Red-Singularity/Led_SnowBoards/_Dustin/media/med.jpg

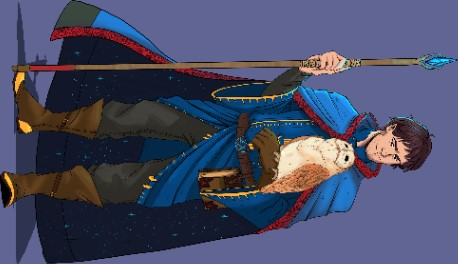
_Dustin/media/med.jpg
