Red-Singularity/Led_SnowBoards/_Dustin/media/mememe.gif

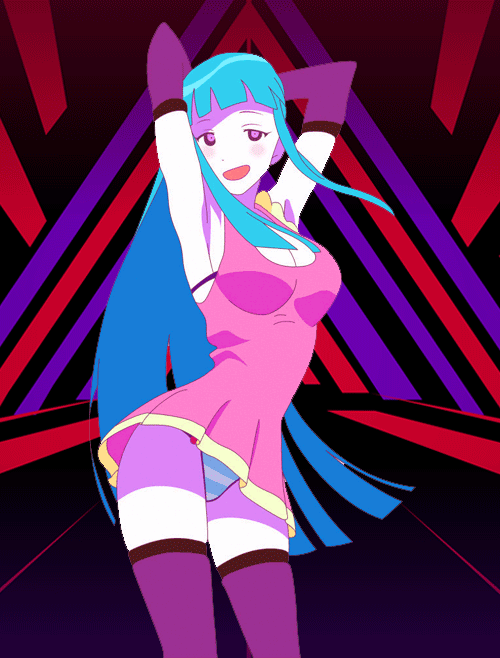
_Dustin/media/mememe.gif
