Red-Singularity/Led_SnowBoards/_Dustin/App Layout V1.png

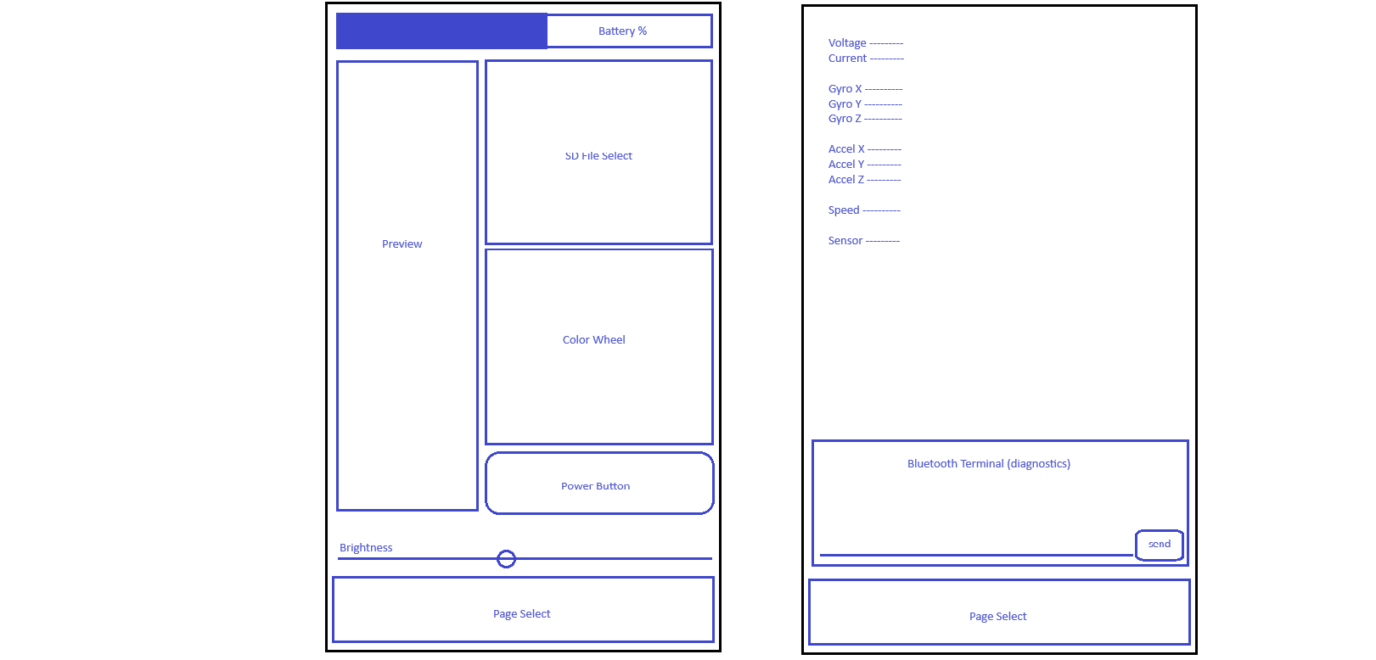
_Dustin/App Layout V1.png
