Red-Singularity/Led_SnowBoards/_Dustin/App Layout V2.jpg

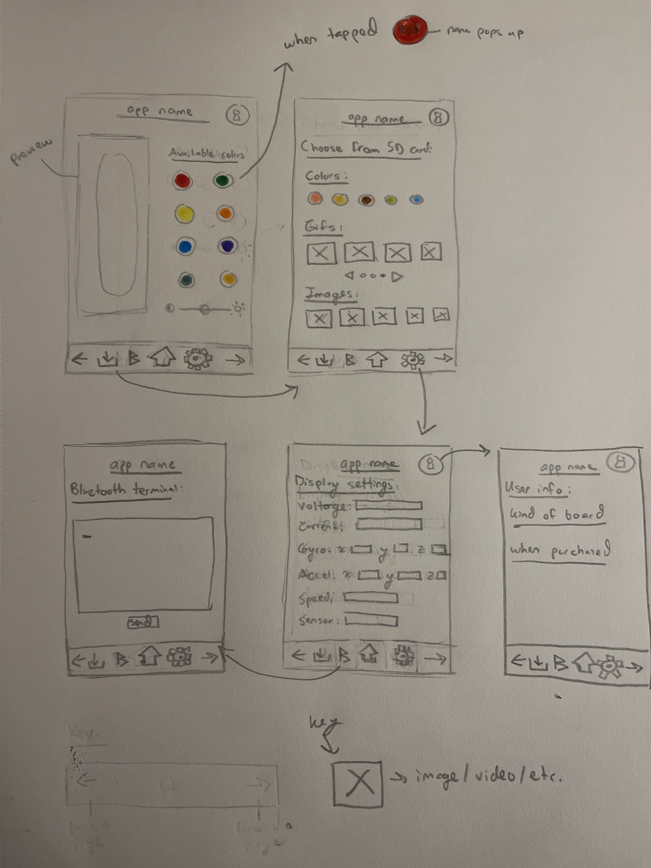
_Dustin/App Layout V2.jpg
