Red-Singularity/Led_SnowBoards/_Dustin/media/amogus.gif

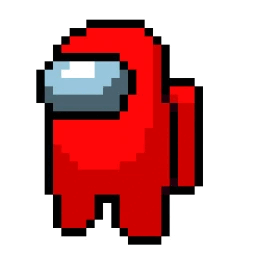
_Dustin/media/amogus.gif
