Red-Singularity/Led_SnowBoards/_Dustin/media/colorwheel.gif

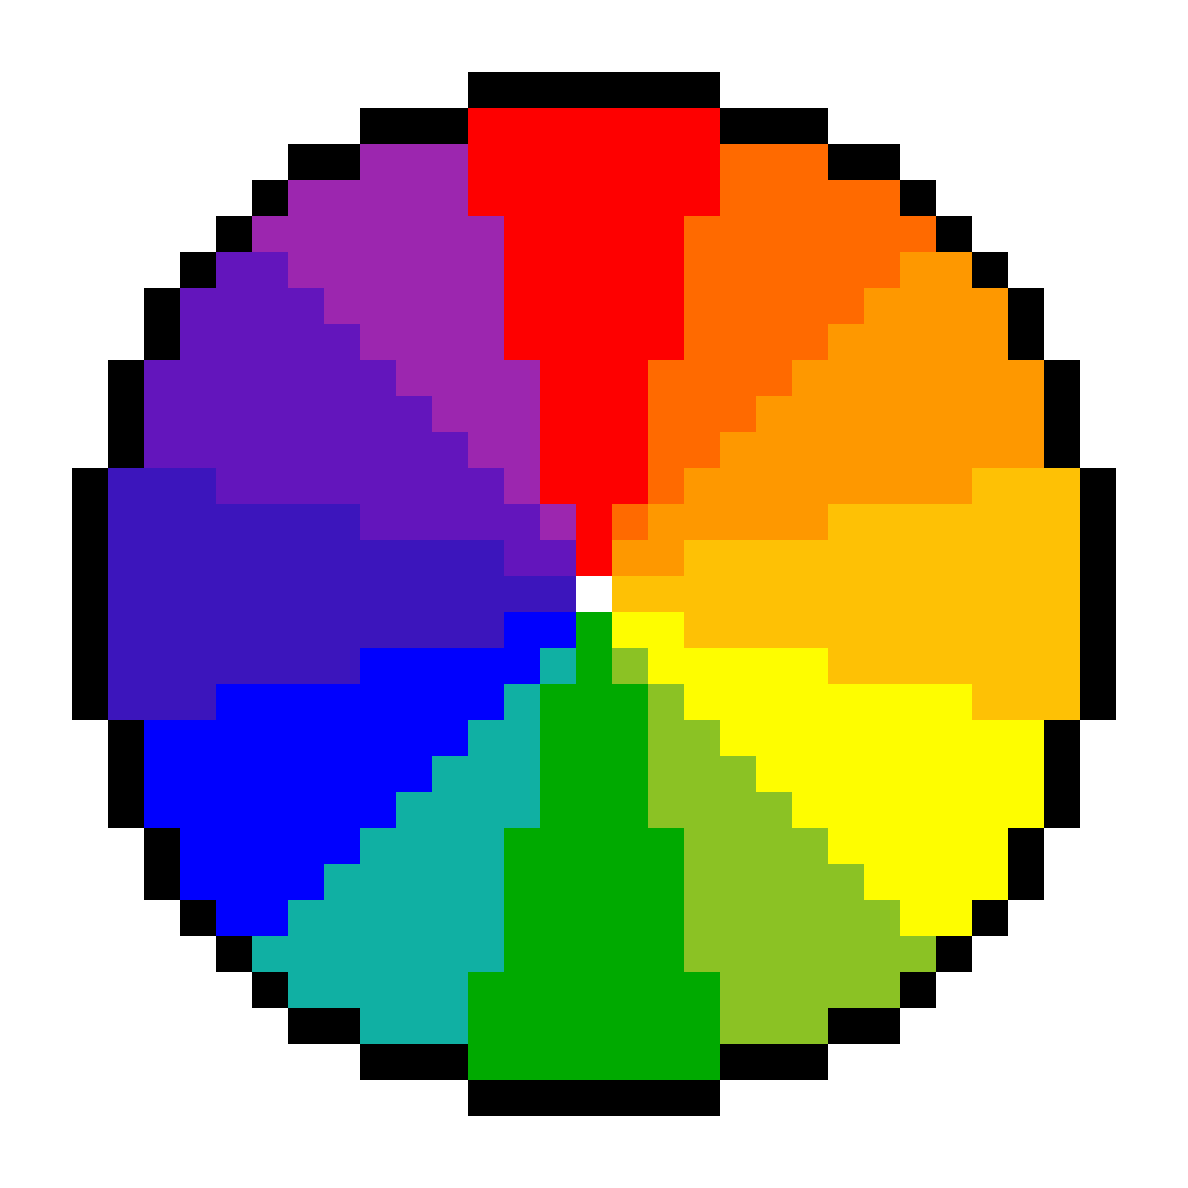
_Dustin/media/colorwheel.gif
