Red-Singularity/Led_SnowBoards/_Dustin/media/link16bit.png

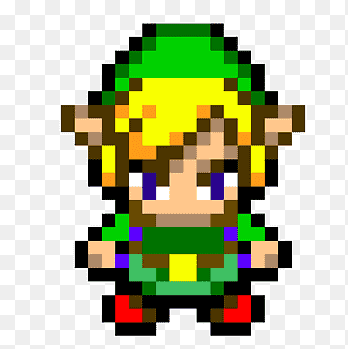
_Dustin/media/link16bit.png
