Red-Singularity/Led_SnowBoards/_Dustin/media/link.png

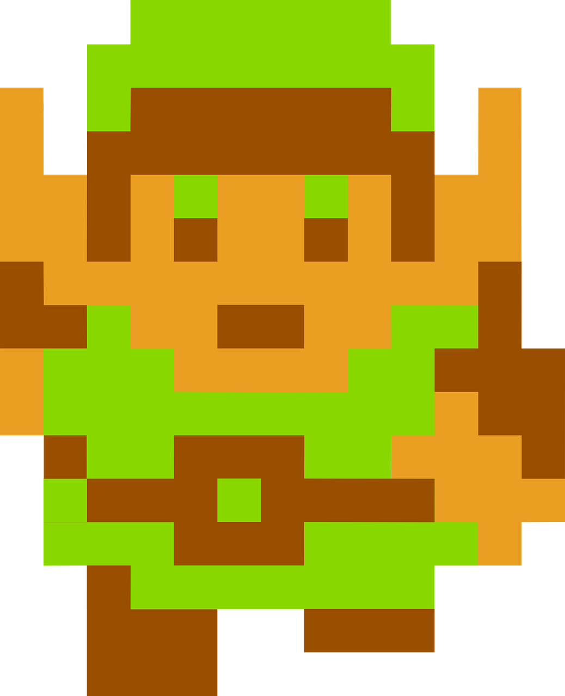
_Dustin/media/link.png
