Red-Singularity/Led_SnowBoards/_Dustin/media/link_s.png

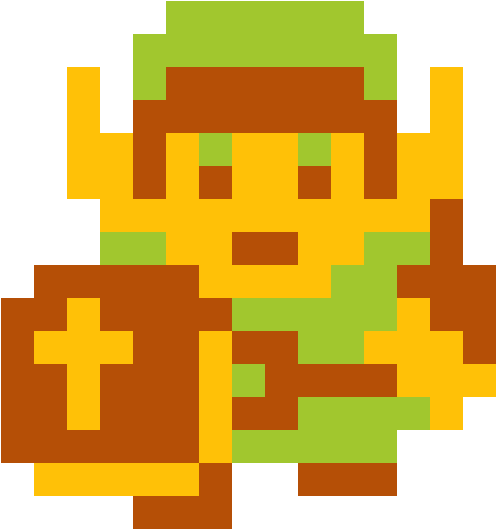
_Dustin/media/link_s.png
