Red-Singularity/Led_SnowBoards/_Dustin/media/mario_characters.gif

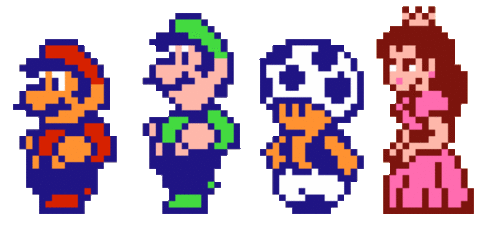
_Dustin/media/mario_characters.gif
