Red-Singularity/Led_SnowBoards/_Dustin/media/rainbow_circle.gif

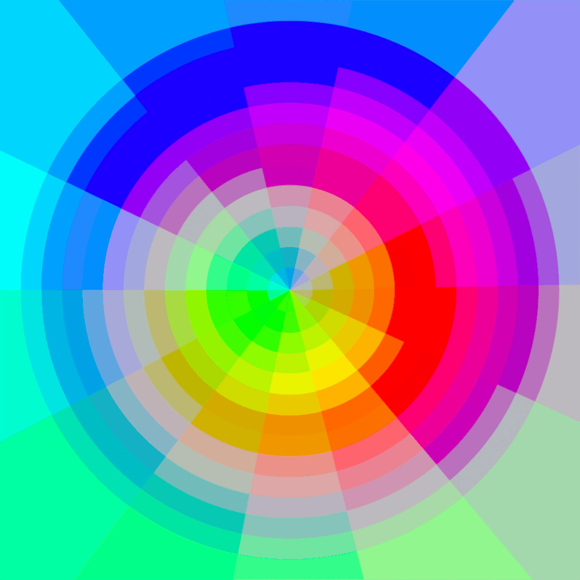
_Dustin/media/rainbow_circle.gif
