Red-Singularity/Led_SnowBoards/_Dustin/media/toothless-dancing.gif

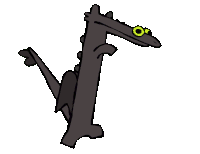
_Dustin/media/toothless-dancing.gif
