Red-Singularity/Led_SnowBoards/_Tim/Snowboard Emulator/processed_Nyan Cat 2.gif

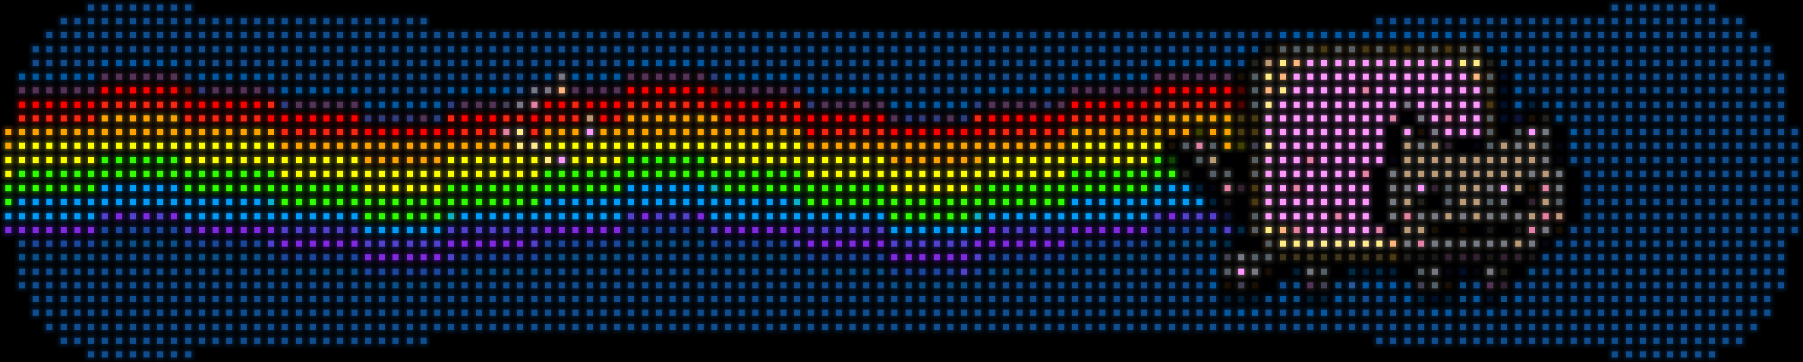
_Tim/Snowboard Emulator/processed_Nyan Cat 2.gif
