Red-Singularity/Led_SnowBoards/_Tim/Snowboard Emulator/Template.png

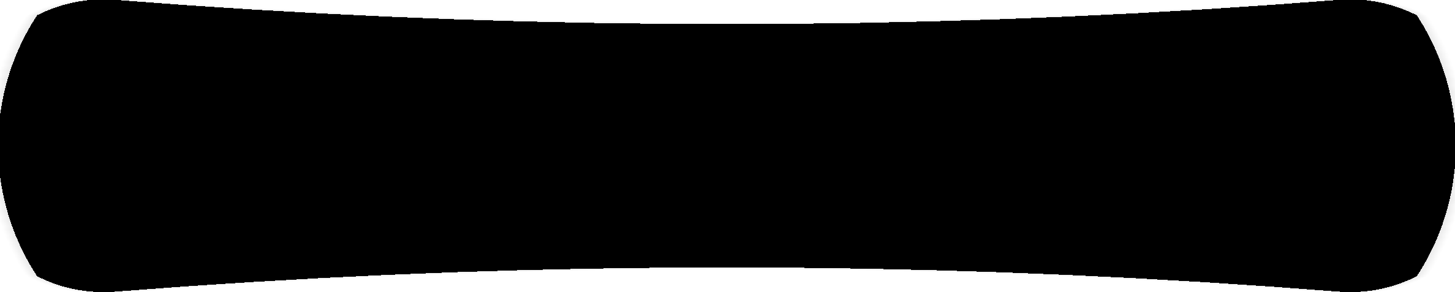
_Tim/Snowboard Emulator/Template.png
