Red-Singularity/Led_SnowBoards/_Dustin/media/test.png

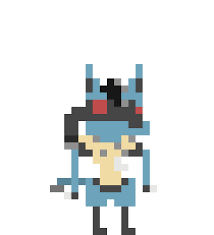
_Dustin/media/test.png
