Red-Singularity/Led_SnowBoards/_Dustin/arduino/sketches/led_snowboard_v2/gif_assignment.ino

void assign_media1(){
  readFrame("media1");
  FastLED.show();
}

void assign_media2(){
  // assign mario from sd card
  readFrame("media2");
  FastLED.show();
}


void assign_media3(){
  // assign pacman from sd card
  readFrame("media3");
  FastLED.show();
}

void assign_media4(){
  // assign neon board from sd card
  readFrame("media4");
  FastLED.show();
}

void assign_media5(){
  // assign neon board from sd card
  readFrame("media5");
  FastLED.show();
}
