Red-Singularity/Led_SnowBoards/_Dustin/arduino/sketches/led_snowboard_v2_debug/gif_assignment.ino

void assign_nyan(){
  // assign nyan cat from sd card
  readFrame("nyan");
  FastLED.show();
}

void assign_mario(){
  // assign mario from sd card
  readFrame("mario");
  FastLED.show();
}


void assign_pacman(){
  // assign pacman from sd card
  readFrame("pacman");
  FastLED.show();
}

void assign_neon(){
  // assign neon board from sd card
  readFrame("The_Heart_of_Neon_board_background");
  FastLED.show();
}

void assign_kirby(){
  // assign neon board from sd card
  readFrame("kirby");
  FastLED.show();
}
