Red-Singularity/Led_SnowBoards/_Dustin/arduino/sketches/gps_test/gps_test.ino

/*
 * Rui Santos 
 * Complete Project Details https://randomnerdtutorials.com
 */
 
#include <SoftwareSerial.h>

// The serial connection to the GPS module
SoftwareSerial ss(16, 17);

void setup(){
  Serial.begin(9600);
  ss.begin(9600);
}

void loop(){
  while (ss.available() > 0){
    // get the byte data from the GPS
    byte gpsData = ss.read();
    Serial.write(gpsData);
  }
}
