Red-Singularity/Led_SnowBoards/_Tim/snowboard_test_code.ino

#include<Wire.h>
#include <FastLED.h>
#define NUM_LEDS 300
#define DATA_PIN 3
#define BRIGHTNESS = 30

#define DEBUG FALSE

// I2C address of the GY-521
const int MPU_addr = 0x68;
int16_t AcX,AcY,AcZ,Tmp,GyX,GyY,GyZ; 

CRGB leds[NUM_LEDS];  //creating memory for LEDs

const int turnSpeed_cutoff = 15000;

void setup(){
  ////setting up GY-521////
  Wire.begin(); 
  Wire.beginTransmission(MPU_addr);
  // PWR_MGMT_1 register 
  Wire.write(0x6B);
  // set to zero (wakes up the GY-521) 
  Wire.write(0); 
  Wire.endTransmission(true); 

  ////setting up LEDs////
  FastLED.addLeds<NEOPIXEL, DATA_PIN>(leds, NUM_LEDS);
  FastLED.setBrightness(30);
  
  Serial.begin(9600);
}

void readGY521(){
  Wire.beginTransmission(MPU_addr);
  // starting with register 0x3B (ACCEL_XOUT_H) 
  Wire.write(0x3B); 
  Wire.endTransmission(false);
  // request a total of 14 registers 
  Wire.requestFrom(MPU_addr,14,true);
  // 0x3B (ACCEL_XOUT_H) & 0x3C (ACCEL_XOUT_L)
  AcX=Wire.read()<<8|Wire.read();
  // 0x3D (ACCEL_YOUT_H) & 0x3E (ACCEL_YOUT_L)
  AcY=Wire.read()<<8|Wire.read();
  // 0x3F (ACCEL_ZOUT_H) & 0x40 (ACCEL_ZOUT_L)
  AcZ=Wire.read()<<8|Wire.read();
  // 0x41 (TEMP_OUT_H) & 0x42 (TEMP_OUT_L)
  Tmp=Wire.read()<<8|Wire.read();
  // 0x43 (GYRO_XOUT_H) & 0x44 (GYRO_XOUT_L)
  GyX=Wire.read()<<8|Wire.read();
  // 0x45 (GYRO_YOUT_H) & 0x46 (GYRO_YOUT_L)
  GyY=Wire.read()<<8|Wire.read();
  // 0x47 (GYRO_ZOUT_H) & 0x48 (GYRO_ZOUT_L)
  GyZ=Wire.read()<<8|Wire.read(); 
  
  #if(DEBUG)
  Serial.print("AcX = "); Serial.print(AcX); Serial.print(" | AcY = "); Serial.print(AcY); Serial.print(" | AcZ = "); Serial.print(AcZ);
  equation for temperature in degrees C from datasheet 
  Serial.print(" | Tmp = "); Serial.print(Tmp/340.00+36.53); 
  Serial.print(" | GyX = "); Serial.print(GyX); Serial.print(" | GyY = "); Serial.print(GyY); Serial.print(" | GyZ = "); Serial.println(GyZ); 
  #endif
}
void loop(){ 
  readGY521();

  if(GyZ > turnSpeed_cutoff){         //turning left
    for(int i = 0; i<=NUM_LEDS; i++){
      leds[i] = CRGB::Blue;
    }
    FastLED.show();
  }
  if(GyZ < -1*turnSpeed_cutoff){      //turning right
    for(int i = 0; i<=NUM_LEDS; i++){
      leds[i] = CRGB::Red;
    }
    FastLED.show();
  }
  if(AcZ > 30000){                    //jumping
   for(int i = 0; i<=NUM_LEDS; i++){
      leds[i] = CRGB::Green;
    }
    FastLED.show();
  }
  delay(10);
}
